Cptmeme/Urmet-Bibus-intercom-tap/firmware/bus_tap_capture/main/wifi.c

#include <string.h>

#include "esp_event.h"
#include "esp_log.h"
#include "esp_netif.h"
#include "esp_wifi.h"
#include "freertos/FreeRTOS.h"
#include "freertos/event_groups.h"
#include "sdkconfig.h"

#include "wifi.h"

static const char *TAG = "wifi";
static EventGroupHandle_t s_events;
#define CONNECTED_BIT BIT0

static void on_event(void *arg, esp_event_base_t base, int32_t id, void *data)
{
    if (base == WIFI_EVENT && id == WIFI_EVENT_STA_START) {
        esp_wifi_connect();
    } else if (base == WIFI_EVENT && id == WIFI_EVENT_STA_DISCONNECTED) {
        xEventGroupClearBits(s_events, CONNECTED_BIT);
        ESP_LOGW(TAG, "disconnected, retrying");
        esp_wifi_connect();
    } else if (base == IP_EVENT && id == IP_EVENT_STA_GOT_IP) {
        const ip_event_got_ip_t *ev = data;
        ESP_LOGI(TAG, "got IP " IPSTR, IP2STR(&ev->ip_info.ip));
        xEventGroupSetBits(s_events, CONNECTED_BIT);
    }
}

void wifi_start(void)
{
    s_events = xEventGroupCreate();
    ESP_ERROR_CHECK(esp_netif_init());
    ESP_ERROR_CHECK(esp_event_loop_create_default());
    esp_netif_t *netif = esp_netif_create_default_wifi_sta();
    /* Must be set before DHCP runs; many routers then resolve bus-tap.<domain>. */
    esp_netif_set_hostname(netif, CONFIG_BUS_TAP_HOSTNAME);

    wifi_init_config_t init = WIFI_INIT_CONFIG_DEFAULT();
    ESP_ERROR_CHECK(esp_wifi_init(&init));
    ESP_ERROR_CHECK(esp_event_handler_register(WIFI_EVENT, ESP_EVENT_ANY_ID, on_event, NULL));
    ESP_ERROR_CHECK(esp_event_handler_register(IP_EVENT, IP_EVENT_STA_GOT_IP, on_event, NULL));

    wifi_config_t cfg = {0};
    strlcpy((char *)cfg.sta.ssid, CONFIG_BUS_TAP_WIFI_SSID, sizeof(cfg.sta.ssid));
    strlcpy((char *)cfg.sta.password, CONFIG_BUS_TAP_WIFI_PASSWORD, sizeof(cfg.sta.password));
    ESP_ERROR_CHECK(esp_wifi_set_mode(WIFI_MODE_STA));
    ESP_ERROR_CHECK(esp_wifi_set_config(WIFI_IF_STA, &cfg));
    ESP_ERROR_CHECK(esp_wifi_start());
    /* Modem sleep adds latency and drops bursts at ~1 Mbit/s sustained. */
    esp_wifi_set_ps(WIFI_PS_NONE);
}

void wifi_wait_connected(void)
{
    xEventGroupWaitBits(s_events, CONNECTED_BIT, pdFALSE, pdTRUE, portMAX_DELAY);
}

int8_t wifi_rssi(void)
{
    wifi_ap_record_t ap;
    return esp_wifi_sta_get_ap_info(&ap) == ESP_OK ? ap.rssi : 0;
}
